paulsammut/ramosclock/images/IMG_1107.JPG

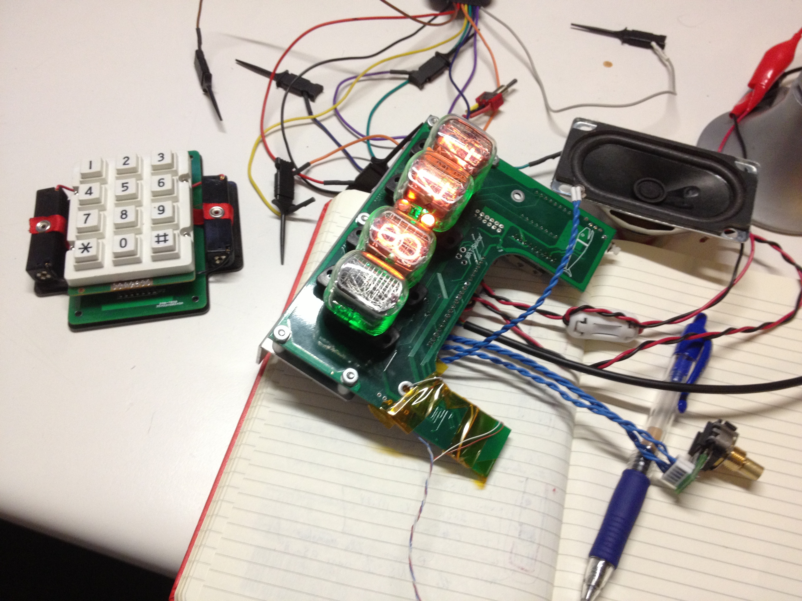
images/IMG_1107.JPG
