paulsammut/ramosclock/images/IMG_1473.jpg

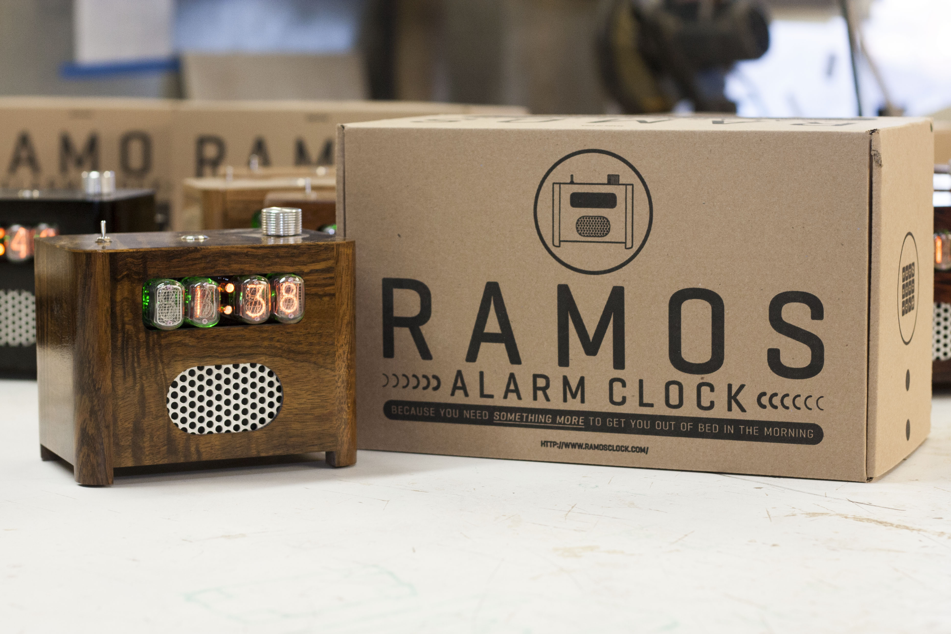
images/IMG_1473.jpg
