paulsammut/ramosclock/images/IMG_1595.JPG

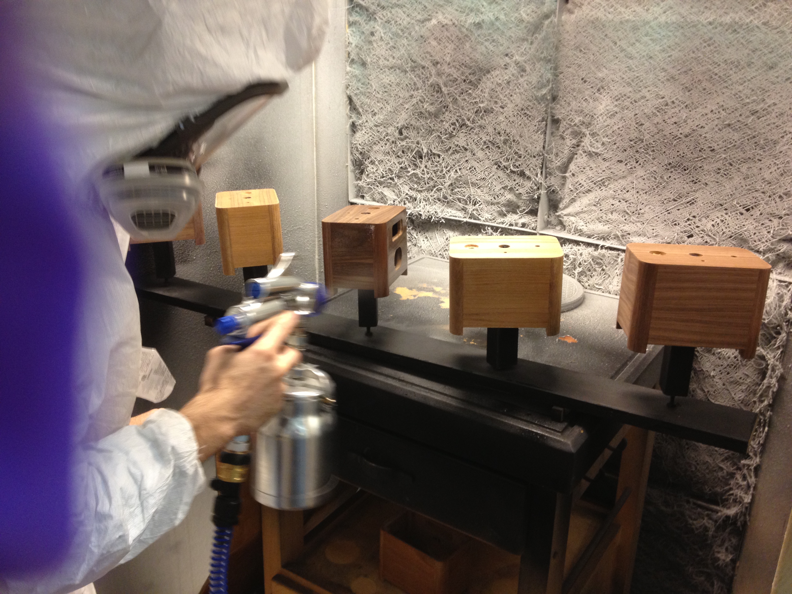
images/IMG_1595.JPG
