paulsammut/ramosclock/images/IMG_2702.JPG

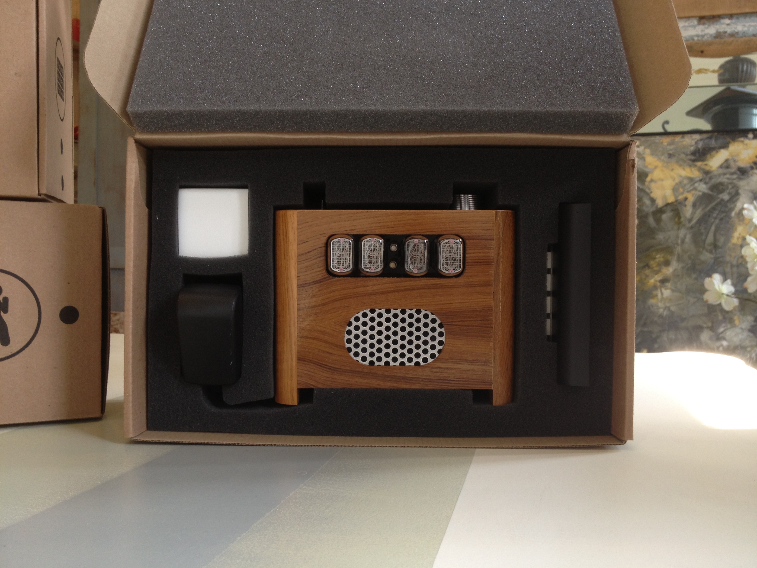
images/IMG_2702.JPG
