paulsammut/ramosclock/Defuse_Panel.X/Too much/lightPlay.h

#ifndef _LIGHTPLAY_H
#define _LIGHTPLAY_H

#include "defusePanel_sys.h"
#include <p18f45k20.h>
#include "defusePanel_sys.h"
#include <delays.h>


void lightPlay(void);
void startUpAnim(void);
void blinkBlue(void);
void blinkRed(void);
void blinkGreen(void);
/**
 * Turns on the light and leaves it solid.
 */
void solidGreen(void);
void solidRed(void);
void solidBlue(void);
void solidOrange(void);
void solidCyan(void);
void solidWhite(void);
void solidPink(void);

#endif
